kerokero5150/GrapplerMinus/Pictures/IMG_8983.jpeg

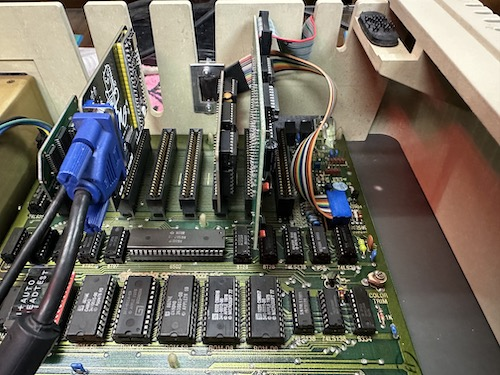
Pictures/IMG_8983.jpeg
